84ace/esp32_battery_isolator/simulations/Draft1.asc

C1: cap; 1µ
C2: cap; 200n
R1: res; 10k
R2: res; 10k
R3: res; 1k
R4: res; 1k
R5: res; 100k
R6: res; 100Meg
R7: res; 1Meg
U1: UniversalOpamp2
U2: UniversalOpamp2
V1: voltage; 3.3V
V2: voltage; SINE(0 1 1k)
Named nets: 0, pos3
.tran 10
