84ace/esp32_battery_isolator/simulations/MOSFET switch circuit.asc

M4: pmos; AONR21357
M5: pmos; AONR21357
Q1: npn; 2N3904
Q4: npn; 2N3904
Q5: pnp; 2N3906
R1: res; 510
R2: res; 10k
R9: res; 0.45
R15: res; 0.04
V5: voltage; 14
V7: voltage; PULSE(0 3.3 0 3ns 3ns 0.1m 0.2m)
Named nets: 0, pos
.tran 1m
.step param pullup 200 2000 600
12.6 to 14.4
PULSE(0 3.3 0 1n 1n {1m-f} {1u+f})
