84ace/esp32_battery_isolator/simulations/psu overvoltage protection.asc

D1: zener; 1N750
R1: res; 1
R2: res; 10
V1: voltage; 4; Rser=.001
Named nets: 0, Vout
.MODEL 1N750 D ( IS=7.035E-16 N=0.9809 BV=3.42 IBV=0.005 RS=0.3487 CJO=3.162E-10 VJ=0.6687 M=0.3164 FC=0.5 mfg=Philips type=zener )
.dc V1 0 6 .25
