84ace/esp32_battery_isolator/lite/simulations/ltspice_batery_switch.asc

I1: load; 25
U2: BSC080N03LS_L0
V1: voltage; 13.8
V2: voltage; 1
Named nets: 0, IN, OUT
.dc step param V2 list 1 2 3 3.3
